Kineticus/Welican_Gemina/Boards/stencilsA.bmp

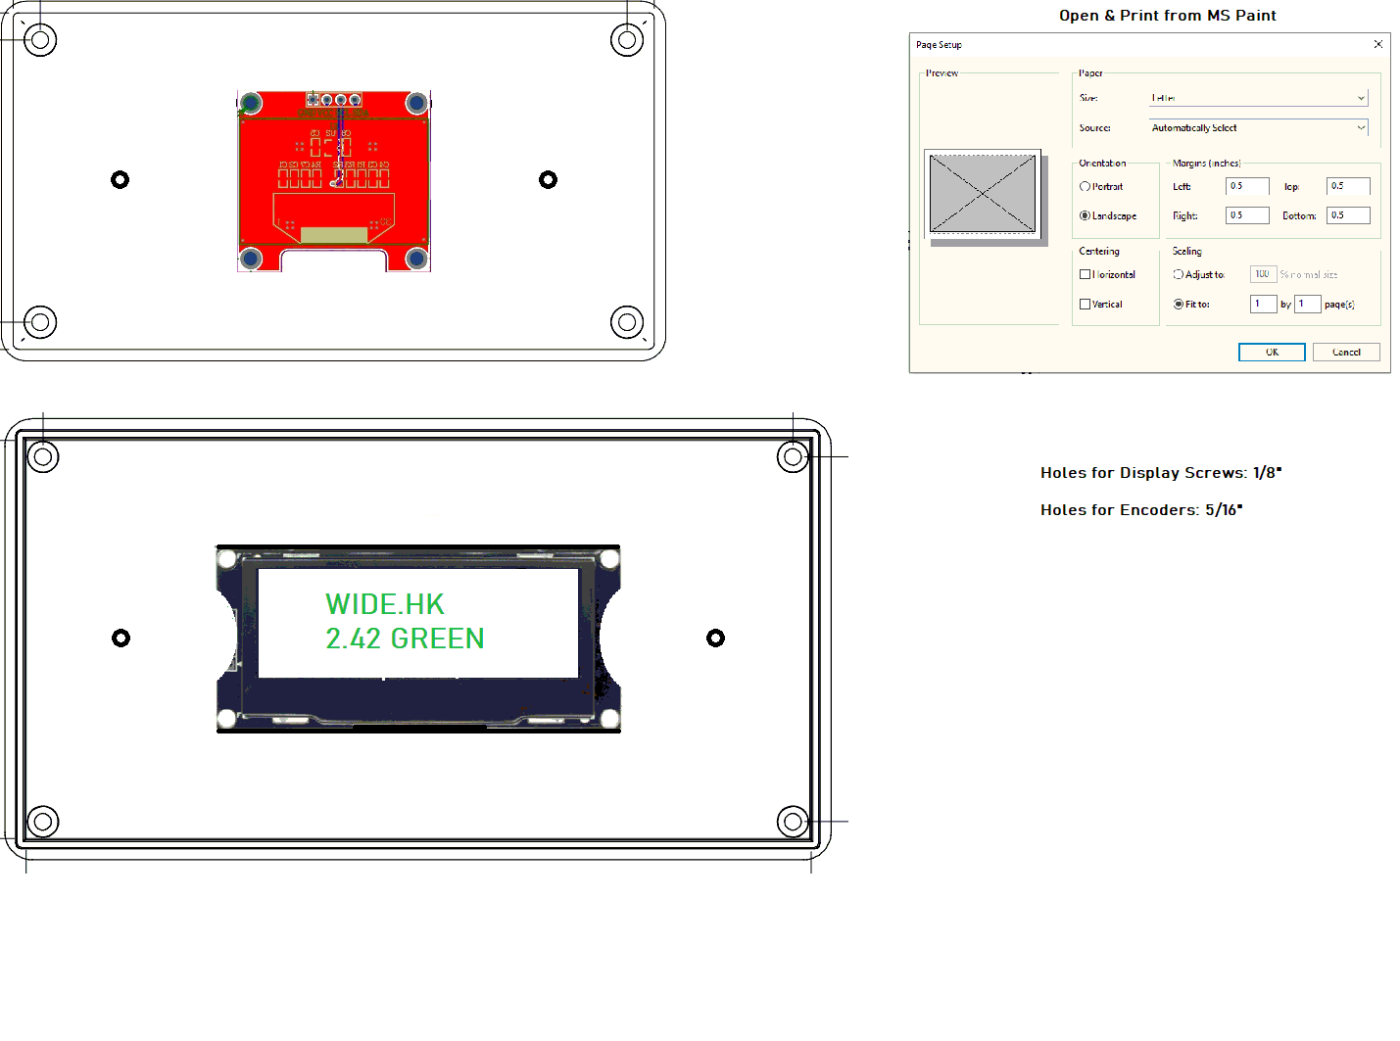
Boards/stencilsA.bmp
