Kineticus/Welican_Gemina/images/test1.bmp

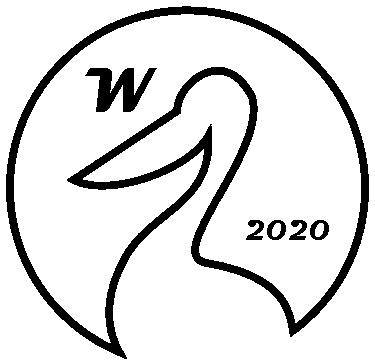
images/test1.bmp
