Kineticus/Welican_Gemina/images.h

// U8X8_PROGMEM
#define WELICAN_LOGO_WIDTH 64
#define WELICAN_LOGO_HEIGHT 64
static const unsigned char WELICAN_LOGO[] = {
    // 'OLED3, 64x64px
    0x00, 0x00, 0x00, 0x00, 0x00, 0x00, 0x00, 0x00, 0x00, 0x00, 0x00, 0x00,
    0x00, 0x00, 0x00, 0x00, 0x00, 0x00, 0x00, 0x00, 0x00, 0x00, 0x00, 0x00,
    0x00, 0x00, 0x00, 0xF8, 0x3F, 0x00, 0x00, 0x00, 0x00, 0x00, 0x80, 0x1F,
    0xF0, 0x03, 0x00, 0x00, 0x00, 0x00, 0xE0, 0x00, 0x00, 0x0E, 0x00, 0x00,
    0x00, 0x00, 0x38, 0x00, 0x00, 0x38, 0x00, 0x00, 0x00, 0x00, 0x06, 0x00,
    0x00, 0xC0, 0x00, 0x00, 0x00, 0x80, 0x03, 0x00, 0x00, 0x80, 0x03, 0x00,
    0x00, 0xC0, 0x00, 0x00, 0x00, 0x00, 0x06, 0x00, 0x00, 0x60, 0x00, 0x00,
    0x00, 0x00, 0x0C, 0x00, 0x00, 0x30, 0x00, 0x00, 0x00, 0x00, 0x18, 0x00,
    0x00, 0x18, 0x00, 0x00, 0x00, 0x00, 0x30, 0x00, 0x00, 0x0C, 0xCF, 0x0C,
    0xF8, 0x00, 0x60, 0x00, 0x00, 0x06, 0xEC, 0x06, 0x8E, 0x01, 0xC0, 0x00,
    0x00, 0x03, 0xEC, 0x02, 0x03, 0x02, 0x80, 0x01, 0x00, 0x01, 0xFC, 0x83,
    0x01, 0x06, 0x00, 0x01, 0x80, 0x01, 0xDC, 0x81, 0x00, 0x0C, 0x00, 0x03,
    0x80, 0x00, 0xCC, 0xC1, 0x18, 0x0C, 0x00, 0x02, 0x40, 0x00, 0xCC, 0x40,
    0x18, 0x08, 0x00, 0x06, 0x40, 0x00, 0x00, 0x60, 0x00, 0x08, 0x00, 0x04,
    0x20, 0x00, 0x00, 0x38, 0x00, 0x0C, 0x00, 0x0C, 0x20, 0x00, 0x00, 0x0C,
    0x00, 0x0C, 0x00, 0x08, 0x30, 0x00, 0x00, 0x07, 0x08, 0x04, 0x00, 0x18,
    0x10, 0x00, 0x80, 0x01, 0x08, 0x04, 0x00, 0x10, 0x10, 0x00, 0xC0, 0x00,
    0x0C, 0x06, 0x00, 0x10, 0x10, 0x00, 0x30, 0x00, 0x0E, 0x02, 0x00, 0x10,
    0x18, 0x00, 0x1C, 0x00, 0x0B, 0x03, 0x00, 0x30, 0x18, 0x00, 0x06, 0xC0,
    0x08, 0x01, 0x00, 0x30, 0x08, 0x80, 0x03, 0x70, 0x88, 0x01, 0x00, 0x20,
    0x08, 0xC0, 0x00, 0x1E, 0x84, 0x00, 0x00, 0x20, 0x08, 0xE0, 0xF1, 0x03,
    0xC4, 0x00, 0x00, 0x20, 0x08, 0x80, 0x3F, 0x00, 0x42, 0x00, 0x00, 0x20,
    0x08, 0x00, 0x00, 0x00, 0x63, 0x00, 0x00, 0x20, 0x08, 0x00, 0x00, 0x80,
    0x21, 0x00, 0x00, 0x20, 0x08, 0x00, 0x00, 0xC0, 0x10, 0x00, 0x00, 0x20,
    0x08, 0x00, 0x00, 0x60, 0x18, 0x00, 0x00, 0x30, 0x18, 0x00, 0x00, 0x18,
    0x08, 0x00, 0x00, 0x30, 0x10, 0x00, 0x00, 0x0C, 0x0C, 0x00, 0x00, 0x10,
    0x10, 0x00, 0x00, 0x06, 0x04, 0x00, 0x00, 0x10, 0x10, 0x00, 0x00, 0x03,
    0x04, 0x00, 0x00, 0x10, 0x30, 0x00, 0x80, 0x01, 0x06, 0x00, 0x00, 0x18,
    0x20, 0x00, 0xC0, 0x00, 0x02, 0x00, 0x00, 0x08, 0x20, 0x00, 0x40, 0x00,
    0x06, 0x00, 0x00, 0x08, 0x60, 0x00, 0x60, 0x00, 0x1C, 0x00, 0x00, 0x0C,
    0x40, 0x00, 0x20, 0x00, 0xF0, 0x01, 0x00, 0x04, 0xC0, 0x00, 0x30, 0x00,
    0x00, 0x07, 0x00, 0x06, 0x80, 0x00, 0x10, 0x00, 0x00, 0x18, 0x00, 0x02,
    0x00, 0x01, 0x10, 0x00, 0x00, 0x70, 0x00, 0x01, 0x00, 0x03, 0x18, 0x00,
    0x00, 0xC0, 0x80, 0x01, 0x00, 0x06, 0x18, 0x00, 0x00, 0x80, 0xC0, 0x00,
    0x00, 0x04, 0x08, 0x00, 0x00, 0x80, 0x61, 0x00, 0x00, 0x08, 0x08, 0x00,
    0x00, 0x00, 0x31, 0x00, 0x00, 0x10, 0x08, 0x00, 0x00, 0x00, 0x1B, 0x00,
    0x00, 0x60, 0x08, 0x00, 0x00, 0x00, 0x0E, 0x00, 0x00, 0xC0, 0x18, 0x00,
    0x00, 0x00, 0x06, 0x00, 0x00, 0x80, 0x11, 0x00, 0x00, 0x00, 0x02, 0x00,
    0x00, 0x00, 0x16, 0x00, 0x00, 0x00, 0x00, 0x00, 0x00, 0x00, 0x3C, 0x00,
    0x00, 0x00, 0x00, 0x00, 0x00, 0x00, 0x30, 0x00, 0x00, 0x00, 0x00, 0x00,
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
};

#define LOCK_WIDTH 9
#define LOCK_HEIGHT 8
static const unsigned char LOCK[] = {
    0x38, 0x00, 0x6C, 0x00, 0x44, 0x00, 0x44, 0x00,
    0xFE, 0x00, 0xEE, 0x00, 0xEE, 0x00, 0xFE, 0x00,
};

#define WIFI_0_WIDTH 9
#define WIFI_0_HEIGHT 8
static const unsigned char WIFI_0[] = {
    0x44, 0x00, 0x28, 0x00, 0x10, 0x00, 0x28, 0x00,
    0x44, 0x00, 0x00, 0x00, 0x10, 0x00, 0x38, 0x00,
};

#define WIFI_1_WIDTH 9
#define WIFI_1_HEIGHT 8
static const unsigned char WIFI_1[] = {
    0x44, 0x00, 0x28, 0x00, 0x10, 0x00, 0x28, 0x00,
    0x44, 0x00, 0x00, 0x00, 0x10, 0x00, 0x38, 0x00,
};

#define WIFI_2_WIDTH 9
#define WIFI_2_HEIGHT 8
static const unsigned char WIFI_2[] = {
    0x00, 0x00, 0x00, 0x00, 0x00, 0x00, 0x00, 0x00,
    0x38, 0x00, 0x44, 0x00, 0x10, 0x00, 0x38, 0x00,
};

#define WIFI_3_WIDTH 9
#define WIFI_3_HEIGHT 8
static const unsigned char WIFI_3[] = {
    0x00, 0x00, 0x00, 0x00, 0x7C, 0x00, 0x82, 0x00,
    0x38, 0x00, 0x44, 0x00, 0x10, 0x00, 0x38, 0x00,
};

#define WIFI_4_WIDTH 9
#define WIFI_4_HEIGHT 8
static const unsigned char WIFI_4[] = {
    0xFE, 0x00, 0x01, 0x01, 0x7C, 0x00, 0x82, 0x00,
    0x38, 0x00, 0x44, 0x00, 0x10, 0x00, 0x38, 0x00,
};

#define DVD_WIDTH 16
#define DVD_HEIGHT 10
static const unsigned char DVD[] = {
    // DVD LOGO, 16x10px
    0x7F, 0xFC, 0xD2, 0x96, 0x92, 0x92, 0x92, 0x93, 0x1F, 0xF9,
    0x00, 0x00, 0x00, 0x00, 0xFC, 0x3F, 0x7F, 0xFC, 0xFC, 0x3F};

#define HEART_WIDTH 8
#define HEART_HEIGHT 8
static const unsigned char HEART[] = {
    0x00, 0x66, 0xFF, 0xFF, 0x7E, 0x3C, 0x18, 0x00,
};

#define MUSIC_NOTE_WIDTH 8
#define MUSIC_NOTE_HEIGHT 8
static const unsigned char MUSIC_NOTE[] = {0xF8, 0xFC, 0x84, 0x84,
                                           0xE4, 0xE7, 0xE7, 0x07};

#define HASHTAG_WIDTH 8
#define HASHTAG_HEIGHT 8
static const unsigned char HASHTAG[] = {
    0xDB, 0xDB, 0x00, 0xDB, 0xDB, 0x00, 0xDB, 0xDB,
};

#define DONUT_WIDTH 8
#define DONUT_HEIGHT 8
static const unsigned char DONUT[] = {
    0x00, 0x3C, 0x42, 0x99, 0xBD, 0x3C, 0x18, 0x00,
};

#define WAVE_WIDTH 8
#define WAVE_HEIGHT 8
static const unsigned char WAVE[] = {
    0x10, 0x14, 0x54, 0x55, 0x55, 0x54, 0x14, 0x10,
};

#define STAR_WIDTH 8
#define STAR_HEIGHT 8
static const unsigned char STAR_SHAPE[] = {
    0x00, 0x00, 0x18, 0x7E, 0x3C, 0x3C, 0x24, 0x00,
};

#define brightness1_width 39
#define brightness1_height 36
static const unsigned char brightness1[] = {
    0x00, 0x00, 0x00, 0x00, 0x00, 0x00, 0x00, 0x00, 0x00, 0x00, 0x00, 0x00,
    0x00, 0x00, 0x00, 0x00, 0x00, 0x00, 0x00, 0x00, 0x00, 0x00, 0x00, 0x00,
    0x00, 0x00, 0x00, 0x00, 0x00, 0x00, 0x00, 0x00, 0x00, 0x00, 0x00, 0x00,
    0x00, 0x00, 0x00, 0x00, 0x00, 0x00, 0x00, 0x00, 0x00, 0x00, 0x00, 0x3F,
    0x00, 0x00, 0x00, 0xC0, 0xFF, 0x00, 0x00, 0x00, 0xE0, 0xC1, 0x01, 0x00,
    0x00, 0x70, 0x80, 0x03, 0x00, 0x00, 0x30, 0x00, 0x03, 0x00, 0x00, 0x30,
    0x00, 0x03, 0x00, 0x00, 0x30, 0x00, 0x03, 0x00, 0x00, 0x30, 0x00, 0x03,
    0x00, 0x00, 0x30, 0x00, 0x03, 0x00, 0x00, 0x70, 0x94, 0x03, 0x00, 0x00,
    0x70, 0x8A, 0x03, 0x00, 0x00, 0x60, 0x94, 0x01, 0x00, 0x00, 0xE0, 0xD2,
    0x01, 0x00, 0x00, 0xC0, 0xD2, 0x00, 0x00, 0x00, 0xC0, 0xE1, 0x00, 0x00,
    0x00, 0x80, 0x61, 0x00, 0x00, 0x00, 0x80, 0x73, 0x00, 0x00, 0x00, 0x80,
    0x7F, 0x00, 0x00, 0x00, 0x00, 0x3F, 0x00, 0x00, 0x00, 0x00, 0x1E, 0x00,
    0x00, 0x00, 0x00, 0x3F, 0x00, 0x00, 0x00, 0x00, 0x02, 0x00, 0x00, 0x00,
    0x00, 0x3D, 0x00, 0x00, 0x00, 0x00, 0x00, 0x00, 0x00, 0x00, 0x00, 0x1E,
    0x00, 0x00, 0x00, 0x00, 0x0C, 0x00, 0x00, 0x00, 0x00, 0x00, 0x00, 0x00,
};

#define brightness2_width 39
#define brightness2_height 36
static const unsigned char brightness2[] = {
    0x00, 0x00, 0x00, 0x00, 0x00, 0x00, 0x00, 0x00, 0x00, 0x00, 0x00, 0x00,
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
  0xFC, 0xFF, 0xFF, 0x1F, 0x00, 0x00, 0x00, 0x00, 0x00, 0x00, 0x00, 0x00, 
  0x00, 0x00, 0x00, 0x00, 0x00, 0x00, 0x00, 0x00, 0x00, 0x00, 0x00, 0x00, 
  0x00, 0x00, 0x00, 0x00, 0x00, 0x00, 0x00, 0x00, 0x00, 0x00, 0x00, 0x00, 
  0x00, 0x00, 0x00, 0x00, 0x00, 0x00, 0x00, 0x00, };
static const unsigned char WEATHER_CLOUDY_23[] = {
  0x00, 0x00, 0x00, 0x00, 0x00, 0x00, 0x00, 0x00, 0x00, 0x00, 0x00, 0x00, 
  0x00, 0x00, 0x00, 0x00, 0x00, 0x00, 0x00, 0x00, 0x00, 0x00, 0x00, 0x00, 
  0x00, 0x00, 0x00, 0x00, 0x00, 0x00, 0x00, 0x00, 0x00, 0xDC, 0x1D, 0x00, 
  0x00, 0x22, 0x22, 0x00, 0x00, 0x41, 0x41, 0x00, 0x00, 0x81, 0x81, 0x00, 
  0xC0, 0x80, 0x80, 0x00, 0x30, 0x01, 0x01, 0x01, 0x08, 0x02, 0x06, 0x06, 
  0x08, 0x00, 0x09, 0x09, 0x04, 0x00, 0x10, 0x10, 0x04, 0x00, 0x10, 0x10, 
  0x04, 0x00, 0x10, 0x10, 0x08, 0x00, 0x10, 0x10, 0x08, 0x00, 0x08, 0x08, 
  0xF0, 0xFF, 0xFF, 0x07, 0x00, 0x00, 0x00, 0x00, 0x00, 0x00, 0x00, 0x00, 
  0x00, 0x00, 0x00, 0x00, 0x00, 0x00, 0x00, 0x00, 0x00, 0x00, 0x00, 0x00, 
  0x00, 0x00, 0x00, 0x00, 0x00, 0x00, 0x00, 0x00, 0x00, 0x00, 0x00, 0x00, 
  0x00, 0x00, 0x00, 0x00, 0x00, 0x00, 0x00, 0x00, };
