Kineticus/Welican_Gemina/magic.h

#define MAGIC_TEXT_SIZE 12

static const unsigned String MAGIC_YES = "Yes";
static const unsigned String MAGIC_NO = "No";
static const unsigned String MAGIC_NOT_SURE = "Not Sure";
static const unsigned String MAGIC_WHO_KNOWS = "Who Knows?";
static const unsigned String MAGIC_GET_A_LIFE = "Get A Life!";
